farmerkeith/Solar-charger-XL4016X2/software/XL4016X2V01/LCDcustom_characters.h

// file created 26 April 2018

//------------------------------------------------------------------------------------------------------
/////////////////////////////////////////BIT MAP ARRAY//////////////////////////////////////////////////
//-------------------------------------------------------------------------------------------------------
byte solar[8] = //icon for solar panel
{
  0b11111,
  0b10101,
  0b11111,
  0b10101,
  0b11111,
  0b10101,
  0b11111,
  0b00000
};

byte battery[8] =
{
  0b01110,
  0b11011,
  0b10001,
  0b10001,
  0b11111,
  0b11111,
  0b11111,
  0b11111,
};

byte _PWM [8] =
{
  0b11101,
  0b10101,
  0b10101,
  0b10101,
  0b10101,
  0b10101,
  0b10101,
  0b10111,
};
